lab11/PlugWatch/powerwatch/hardware/plugwatch_D/board/README.md

# Electron Sensor Board Rev 4
This sensor board is part of the [GridWatch](http://grid.watch) project.

The goal of this board is to test data collection in Accra. It is an updated
version of revision 3 with a focus on reliable operation even with a lack
of power and cloud connectivity. Please reference revision three for more
information.
