lab11/PlugWatch/powerwatch/firmware/particle/plugwatch_F/README.md

Plugwatch F Firmware
====================

We are building and deploying 400 of Plugwatch F.

It is hardware revision 1 in the versioning system (i.e. firmwares starting at 000100).

With plugwatch F the data format changes to include voltage and test whether the device
is plugged in or not.
