lab11/PlugWatch/powerwatch/cloud/kubernetes/grafana/README.md

Timescale
=================================

To deploy the grafana instance follow these steps:

## Setup a configuration file

```
$ kubectl create configmap grafana-provisioning --from-file=datasource.yaml --from-file=dashboard.yaml
$ kubectl create configmap grafana-dashboards --from-file=Powerwatch_General.json
```

## Add secrets

Modify the secrets files to add the database usernames and passwords

```
$ kubectl create -f ./grafana-config.yaml
```

## Deploy the cluster
```
$ kubectl create -f ./grafana-deployment.yaml
```
