lab11/PlugWatch/app/src/main/ic_launcher-web.png

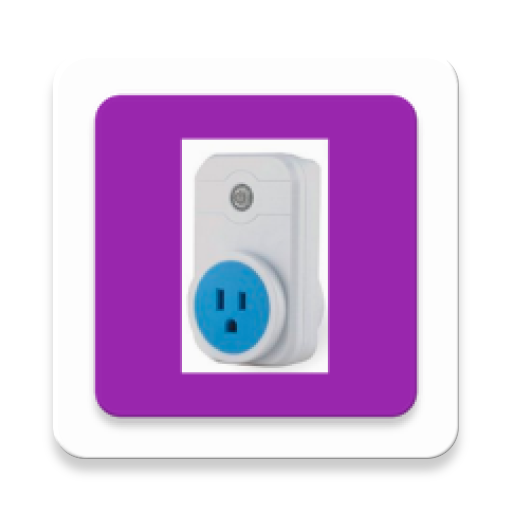
app/src/main/ic_launcher-web.png
