lab11/PlugWatch/powerwatch/deployment-tools/provision/base_tag.png

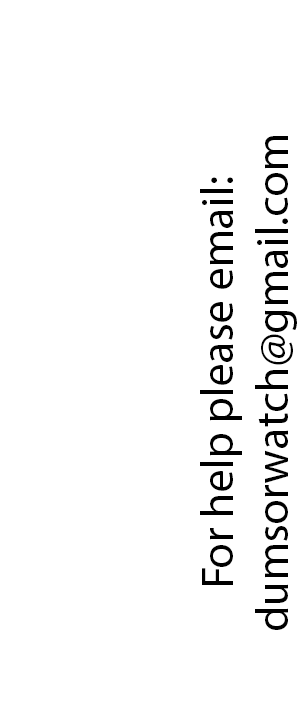
powerwatch/deployment-tools/provision/base_tag.png
