lab11/PlugWatch/powerwatch/deployment-tools/provision/wit/code.png

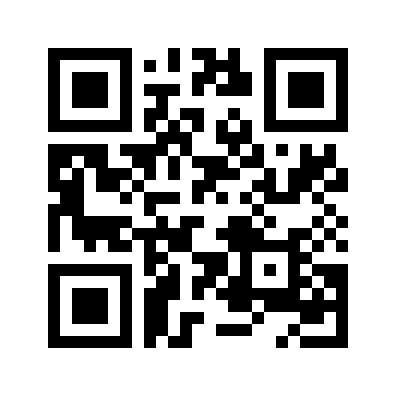
powerwatch/deployment-tools/provision/wit/code.png
