lab11/PlugWatch/powerwatch/hardware/electron_rev_1/board_image.png

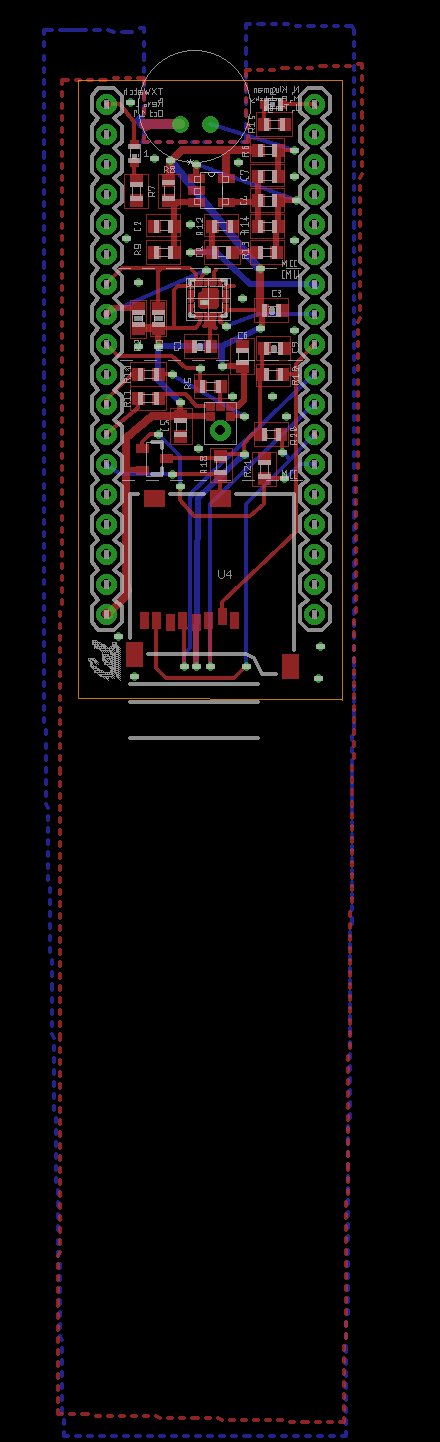
powerwatch/hardware/electron_rev_1/board_image.png
