lab11/PlugWatch/powerwatch/hardware/plugwatch_E/board/plugwatch_pcb.png

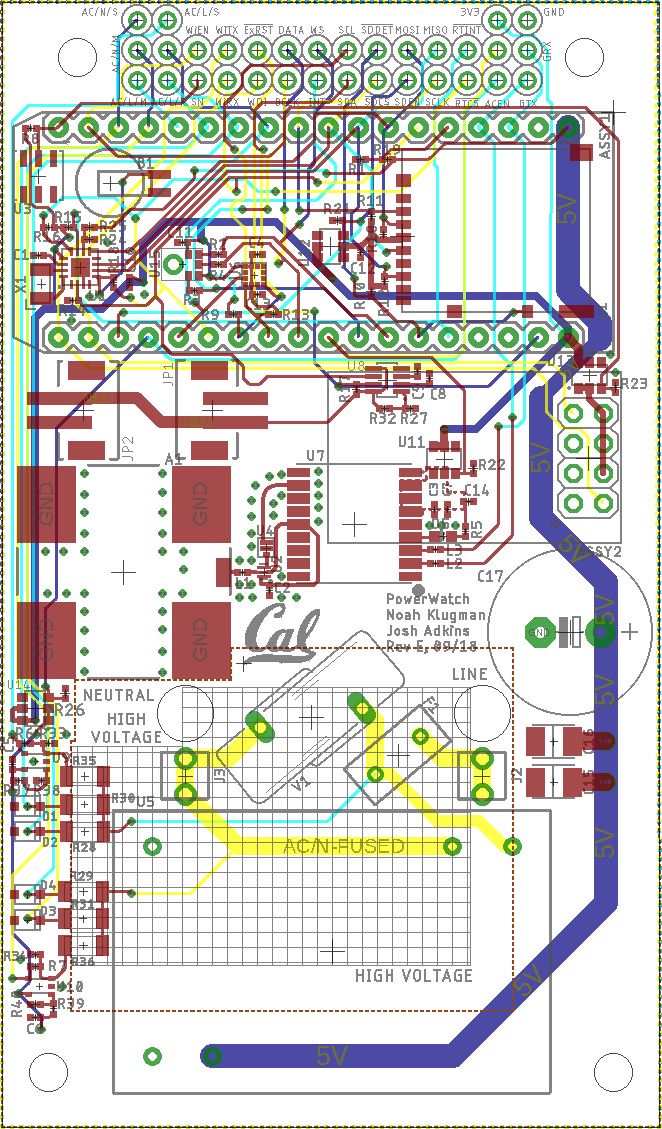
powerwatch/hardware/plugwatch_E/board/plugwatch_pcb.png
