lab11/PlugWatch/powerwatch/hardware/electron_rev_1/orders/costs.xlsx

Order | Cost | Submitted | Reimbursed | Shipment Expected | Received | Item | Num Units | Per Unit | Total
Particle | 1332.38 | No | No | unknown | No | particles | 15 | 170.8206667 | 2562.31
Sparkfun | 275.75 | No | No | 25th | No | sd sockets, test parts, gas sensors
Digikey | 349.75 | No | No |  | No | resistors, capacitors, imu, microphones, op-amps, mosfets
PCB | 237 | No | No |  | No | 15 circuit boards
Amazon | 237.44 | No | No | 22nd | 22nd | sd cards
Particle | 129.99 | No | No | Preorder | No | enterprise eval kit
