lab11/PlugWatch/powerwatch/hardware/electron_rev_1/orders/amazon_order.png

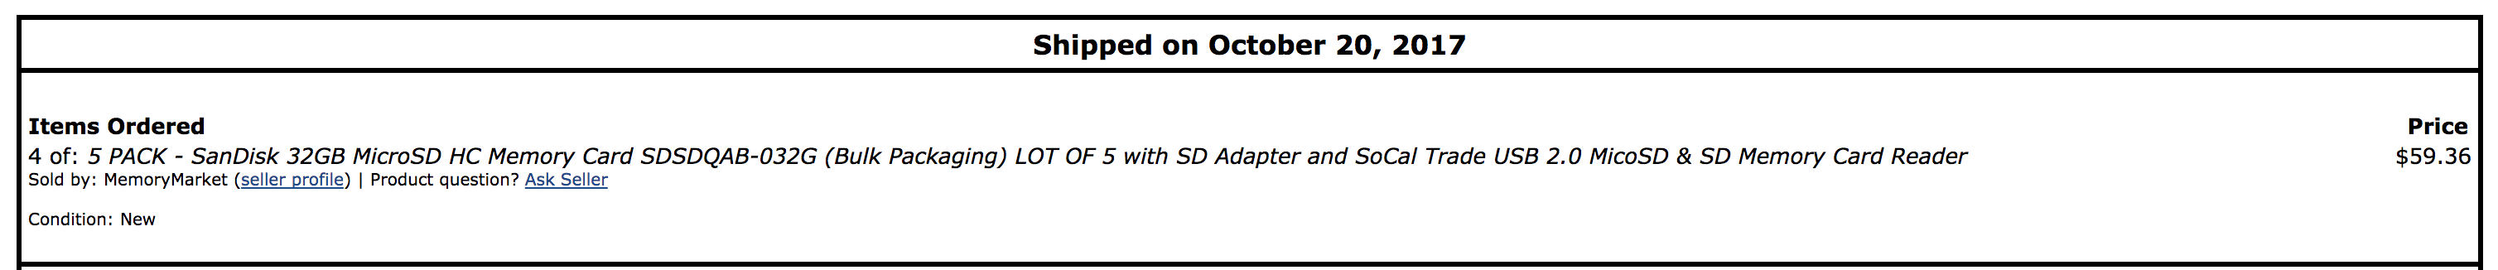
powerwatch/hardware/electron_rev_1/orders/amazon_order.png
