lab11/PlugWatch/powerwatch/hardware/plugwatch_B/case/particle_base.SLDPRT

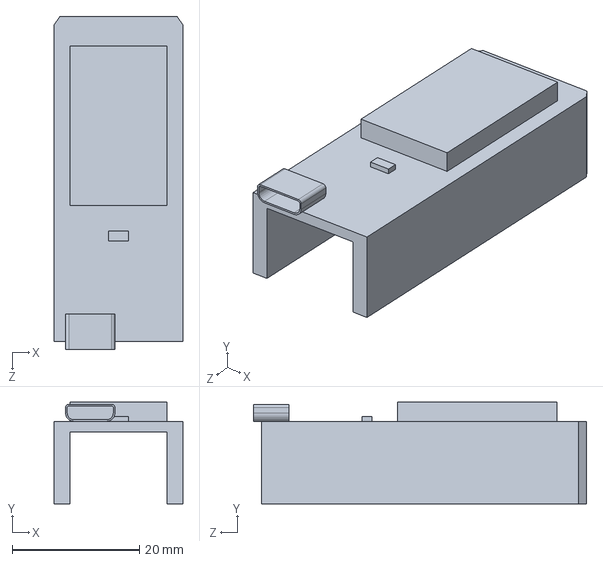
[picture p25: CAD file, 2018-01-17]
powerwatch/hardware/plugwatch_B/case/particle_base.SLDPRT
20.2 x 16.0 x 52.2 mm
