lab11/PlugWatch/powerwatch/hardware/plugwatch_B/case/battery.SLDPRT

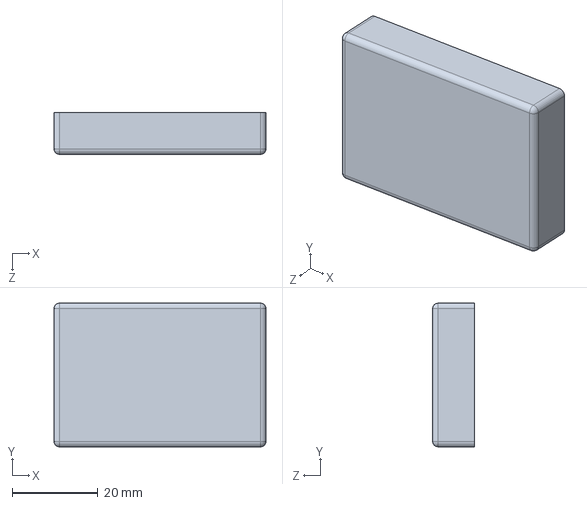
[picture p26: CAD file, 2018-01-17]
powerwatch/hardware/plugwatch_B/case/battery.SLDPRT
49.4 x 33.5 x 9.73 mm
