lab11/PlugWatch/powerwatch/hardware/plugwatch_D/board/plugwatch.pdf

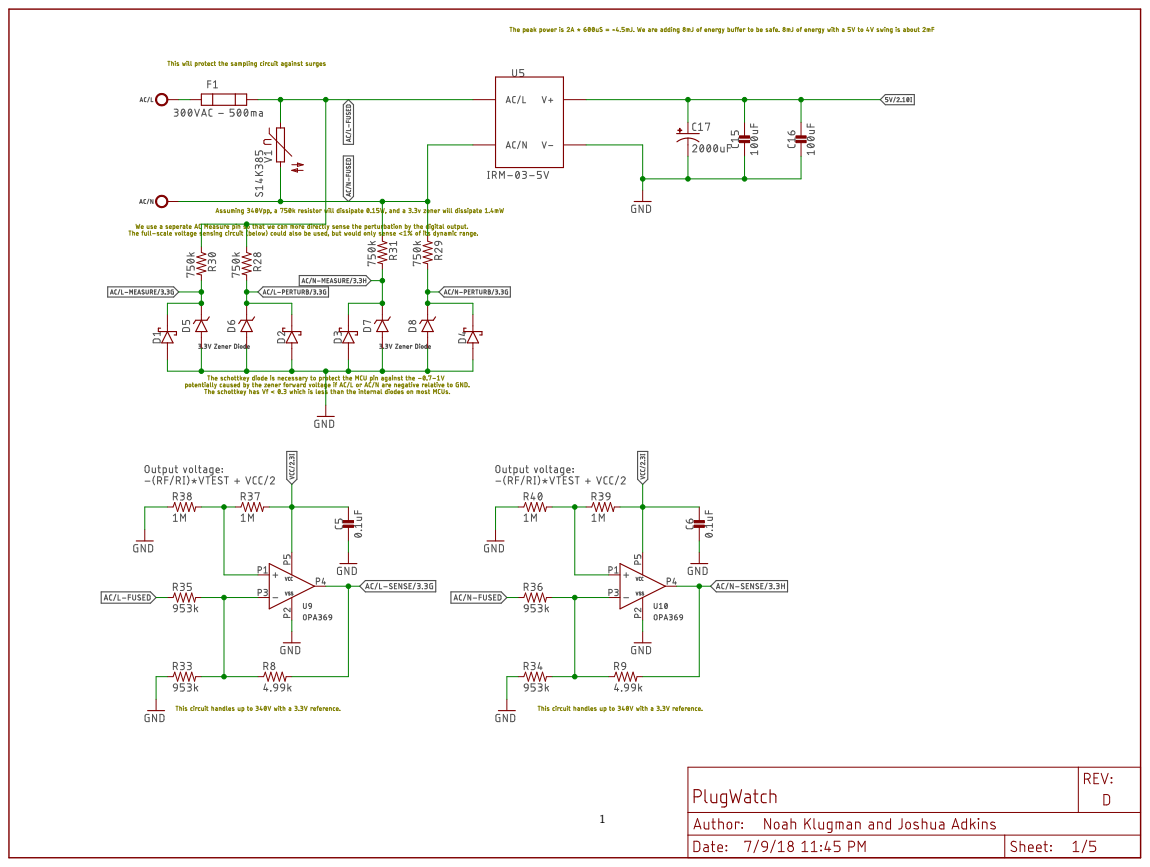
[picture p64: page 1]

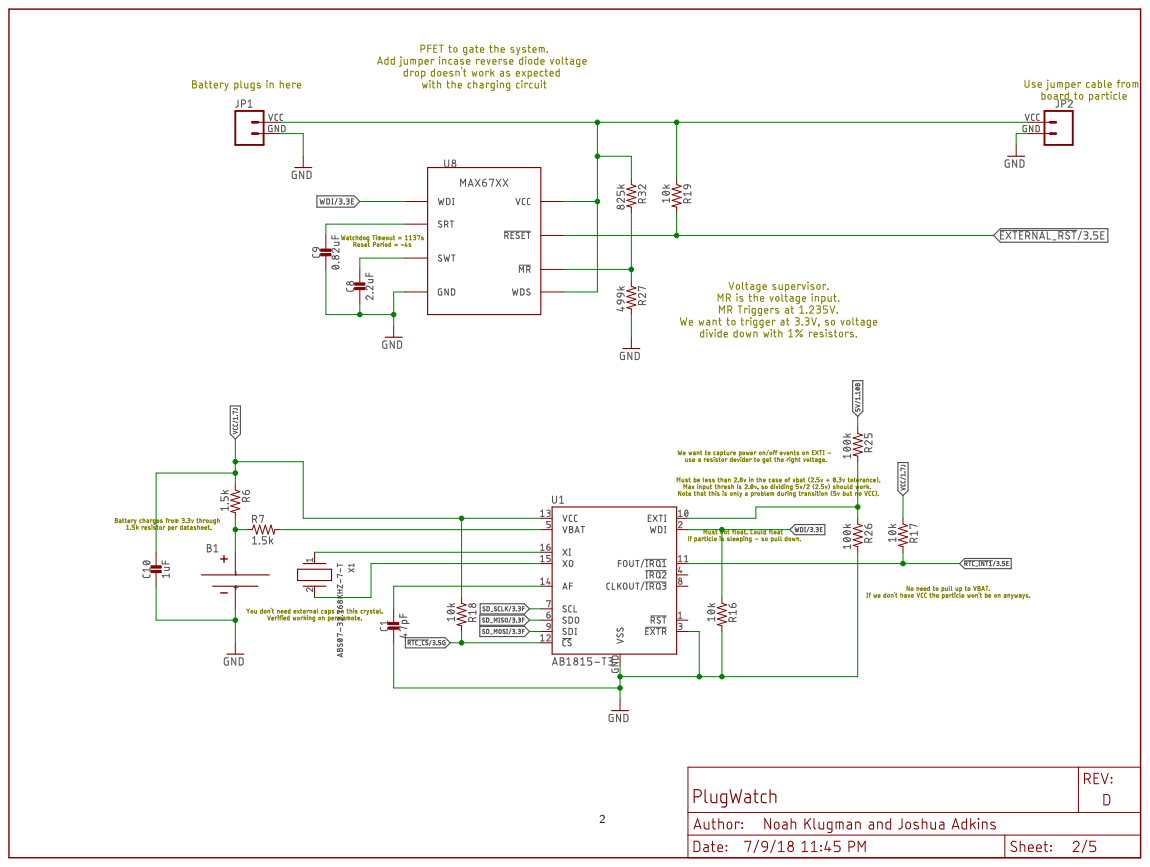
[picture p65: page 2]

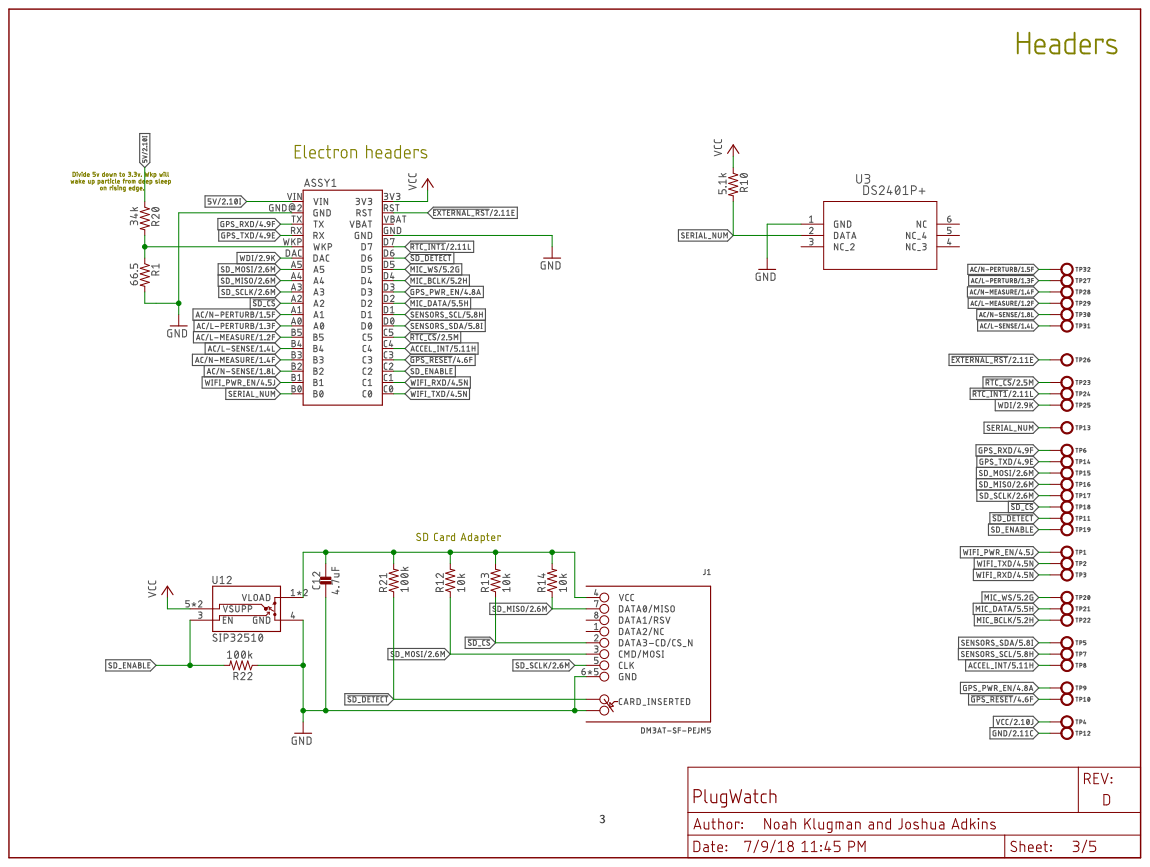
[picture p66: page 3]

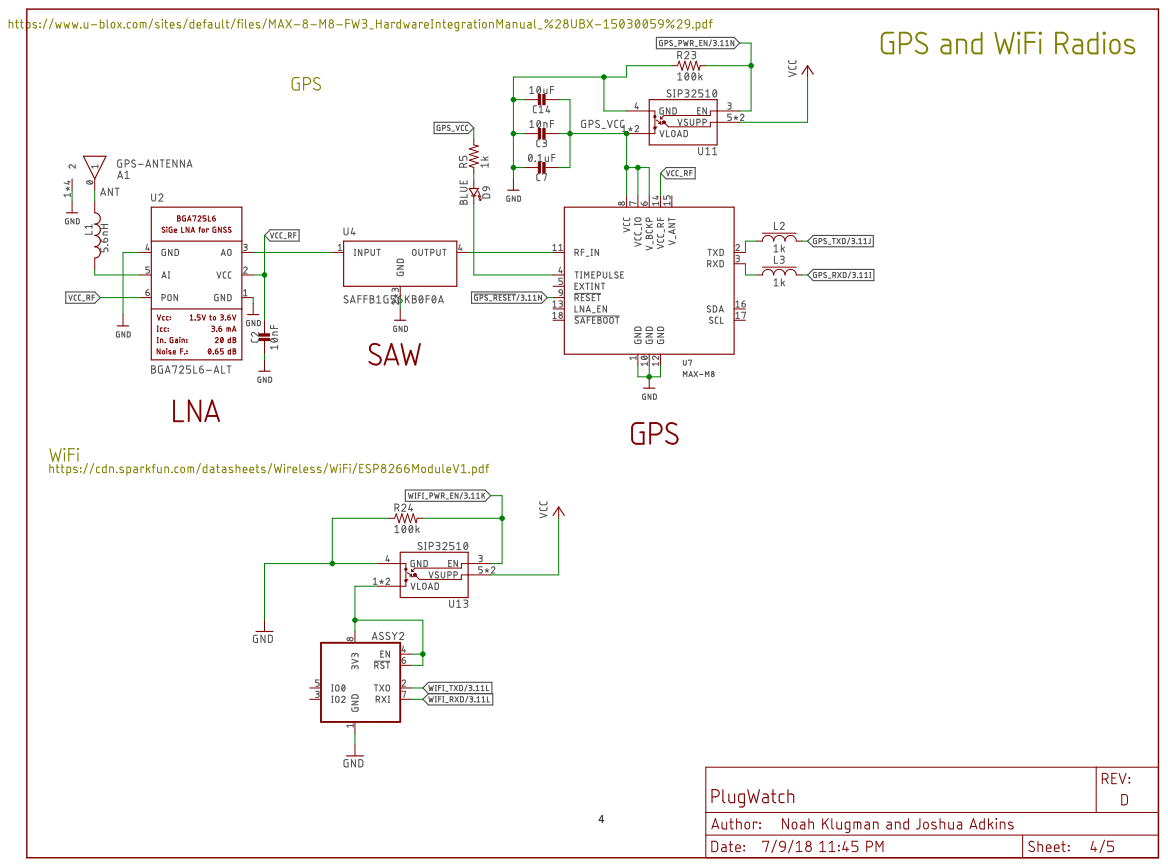
[picture p67: page 4]

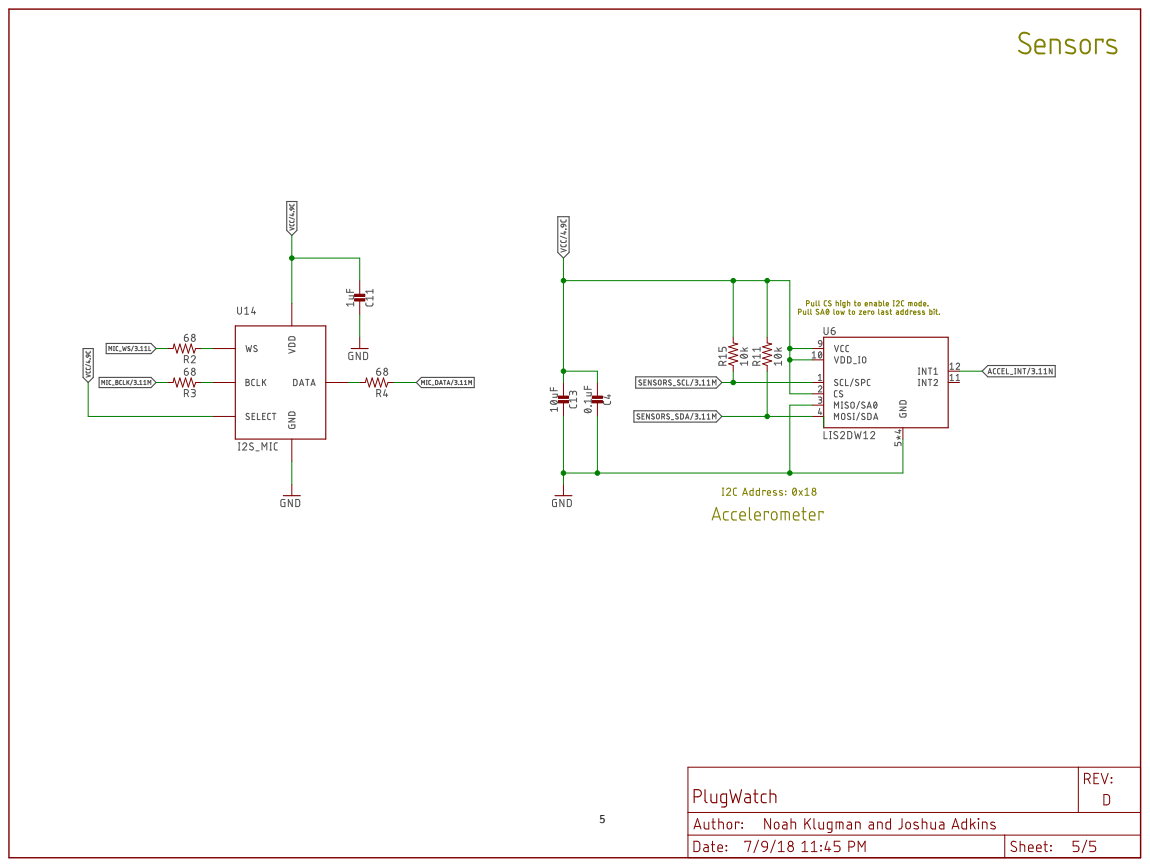
[picture p68: page 5]

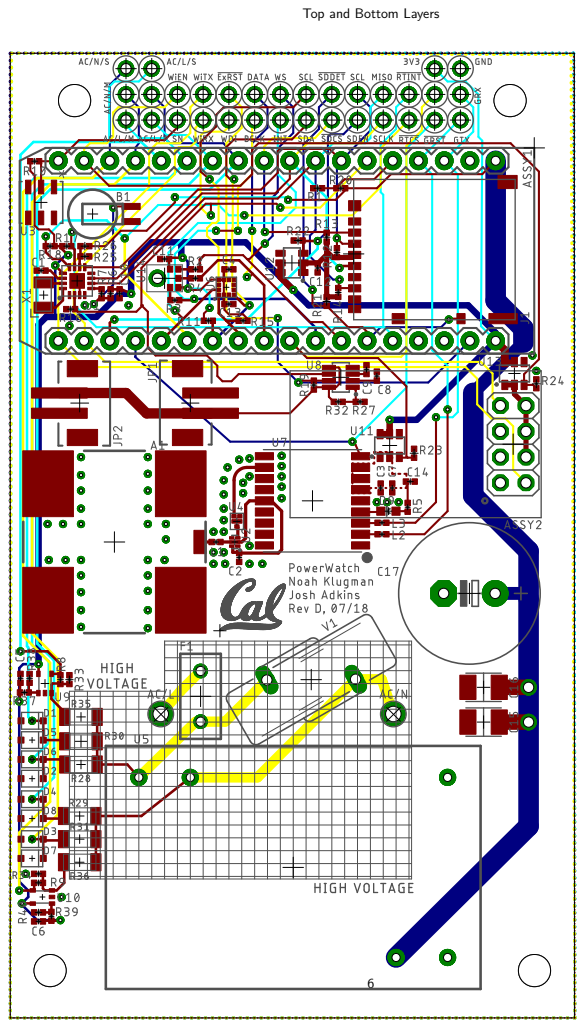
[picture p69: page 6]

Top and Bottom Layers

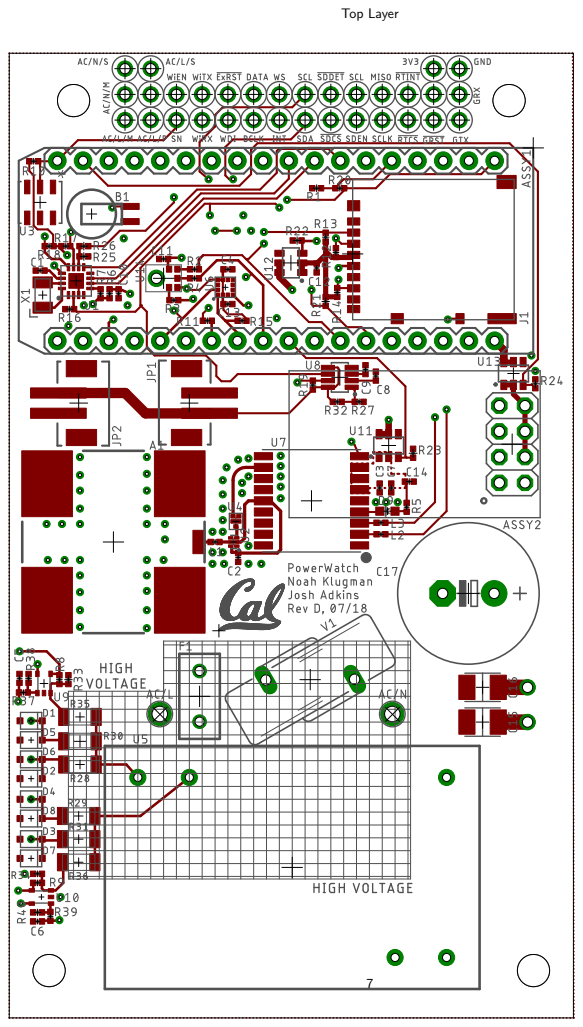
[picture p70: page 7]
Top Layer

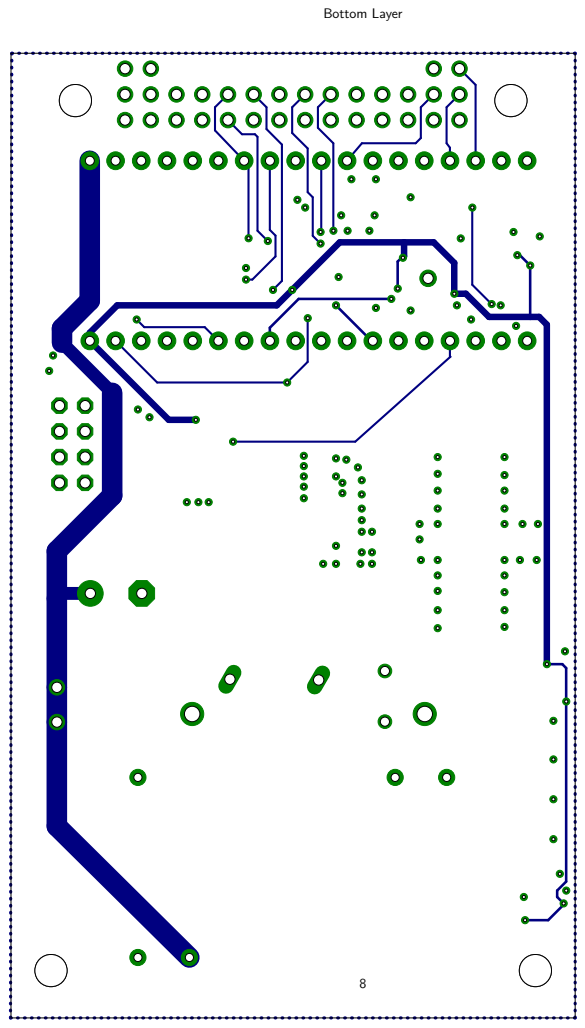
[picture p71: page 8]
Bottom Layer

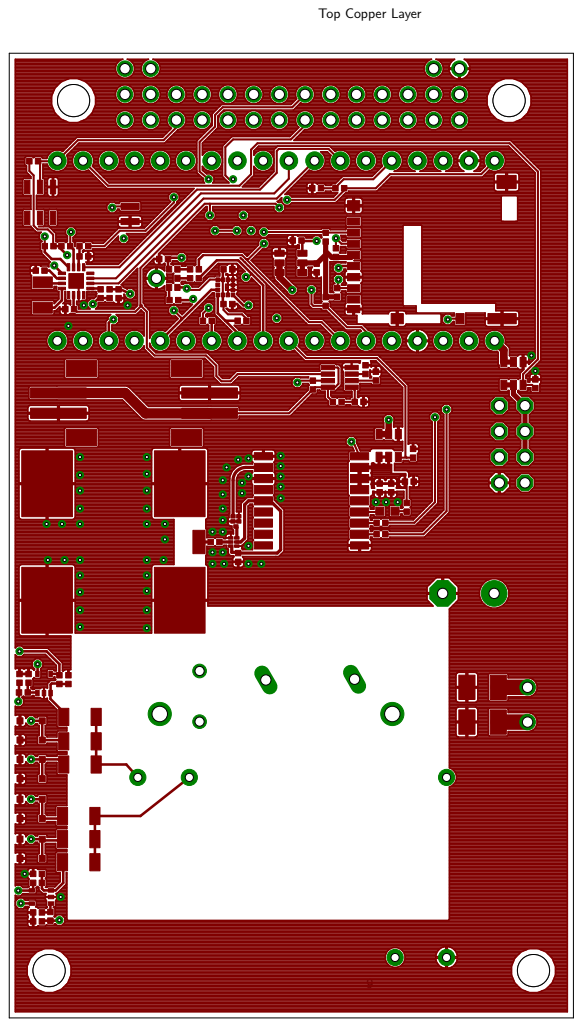
[picture p72: page 9]

Top Copper Layer

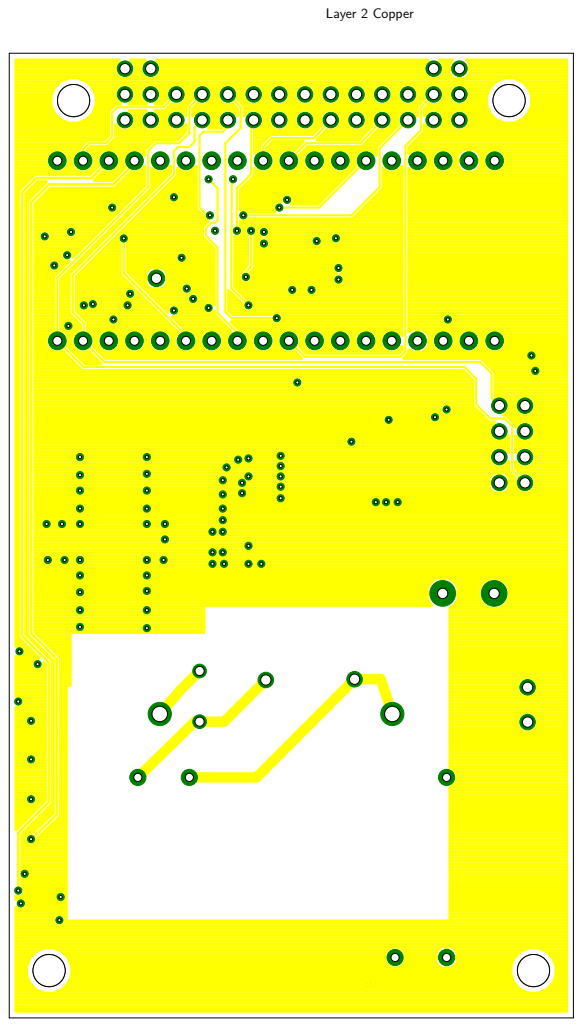
[picture p73: page 10]
Layer 2 Copper

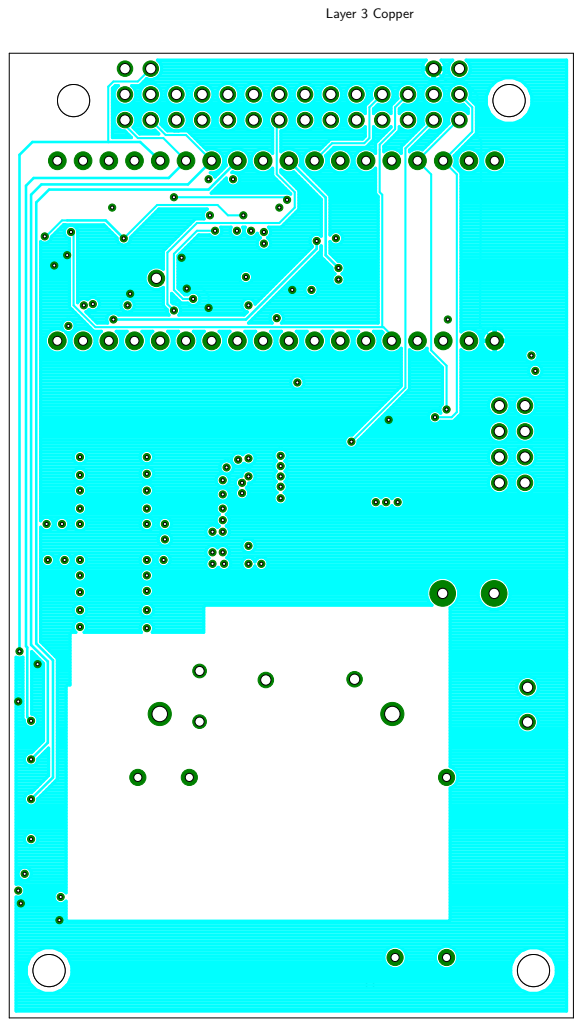
[picture p74: page 11]
Layer 3 Copper

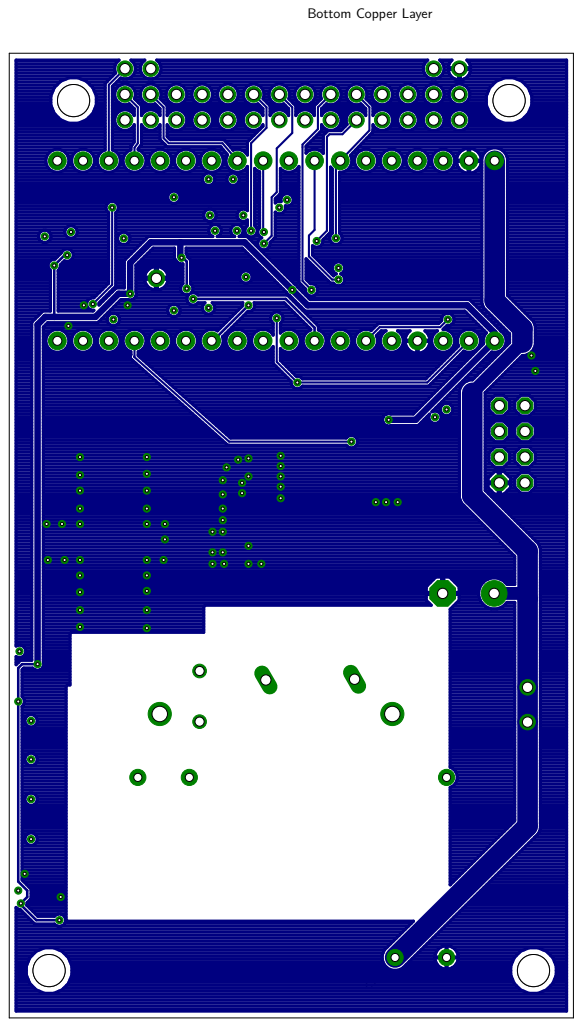
[picture p75: page 12]

Bottom Copper Layer

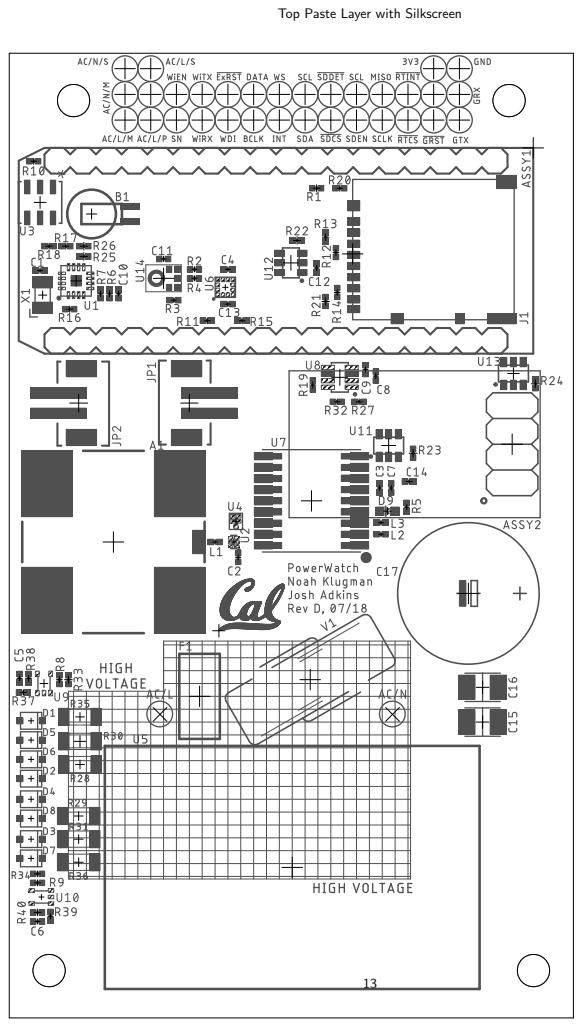
[picture p76: page 13]

Top Paste Layer with Silkscreen

Bottom Paste Layer with Silkscreen

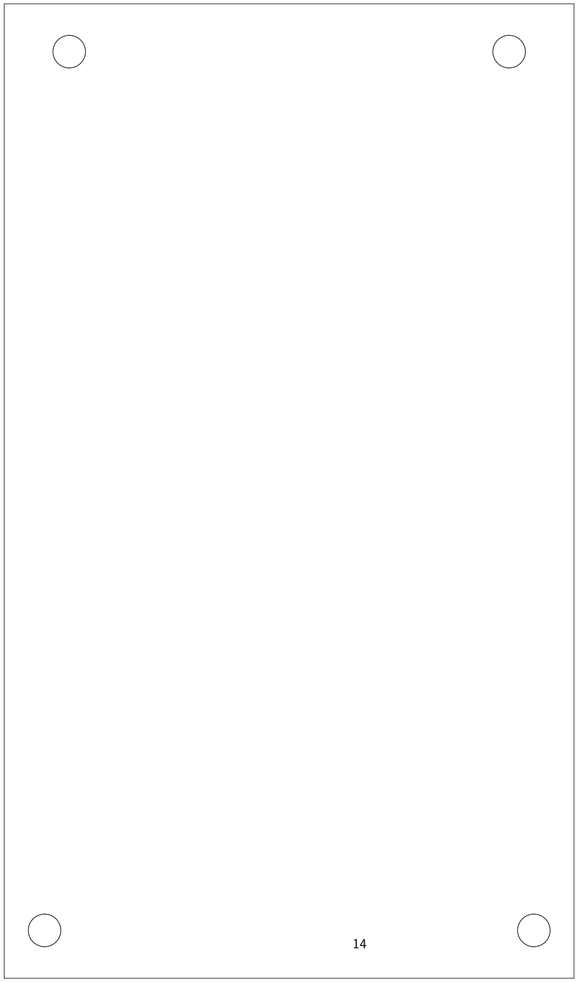
[picture p77: figure]
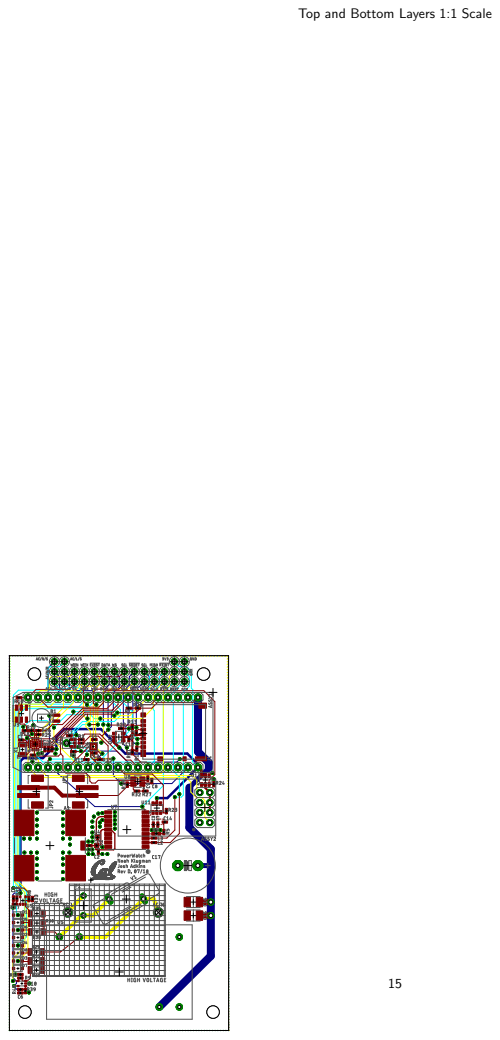
[picture p78: page 15]

Top and Bottom Layers 1:1 Scale

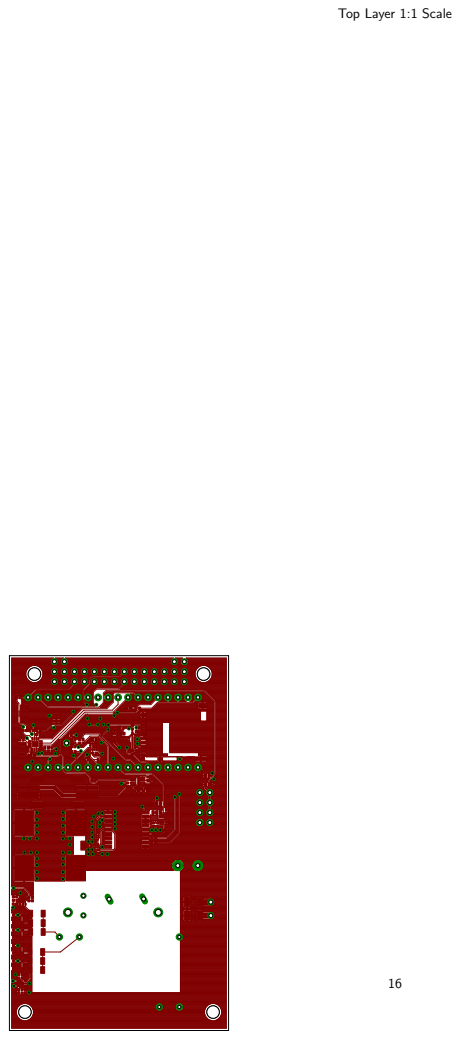
[picture p79: page 16]

Top Layer 1:1 Scale

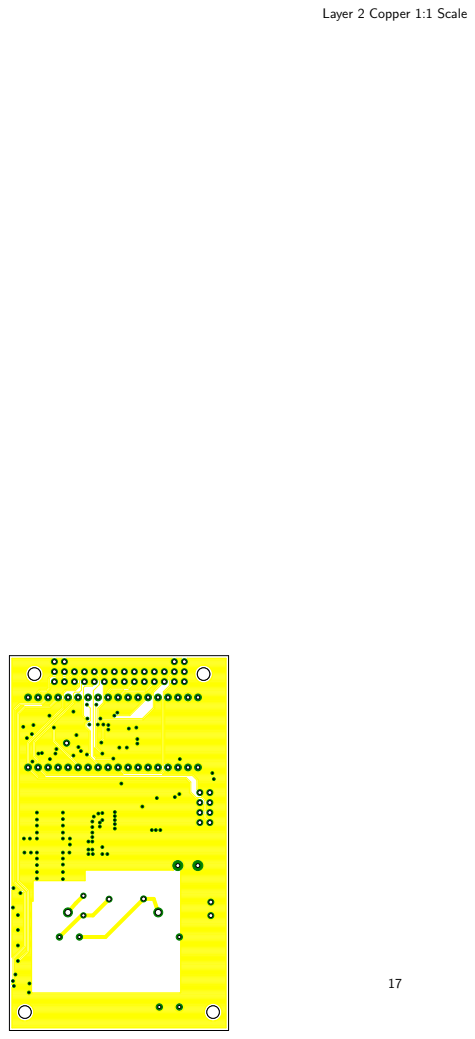
[picture p80: page 17]

Layer 2 Copper 1:1 Scale

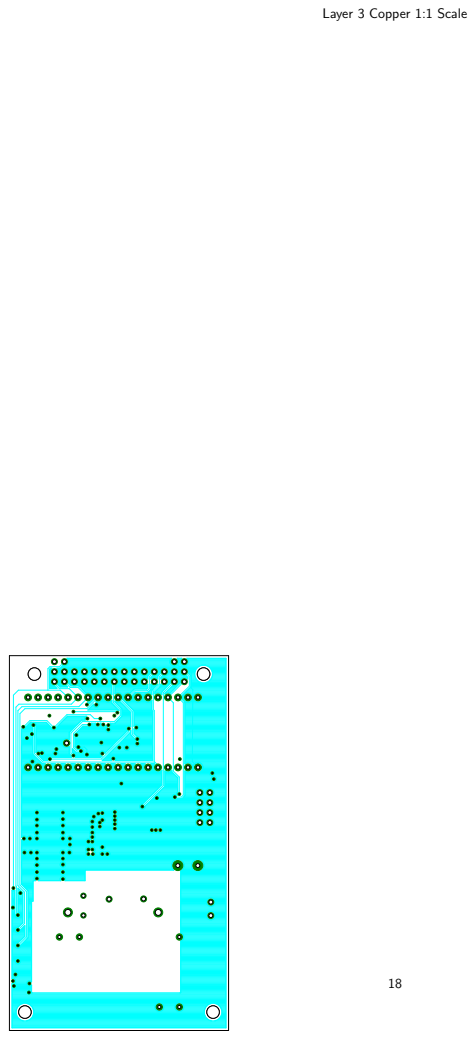
[picture p81: page 18]

Layer 3 Copper 1:1 Scale

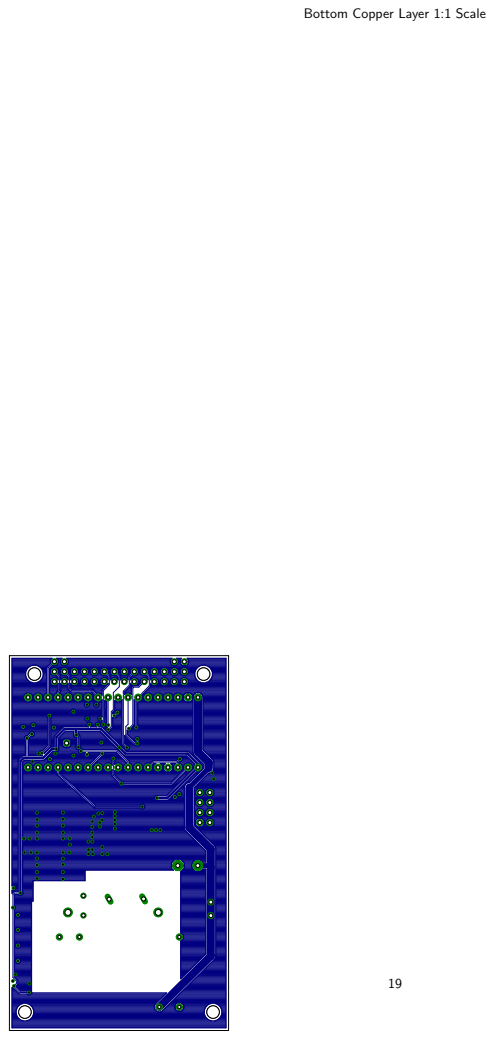
[picture p82: page 19]

Bottom Copper Layer 1:1 Scale
