lab11/PlugWatch/Data/kplc_interruption/Interruptions/Special_Interruption_in_Western_Kenya.pdf

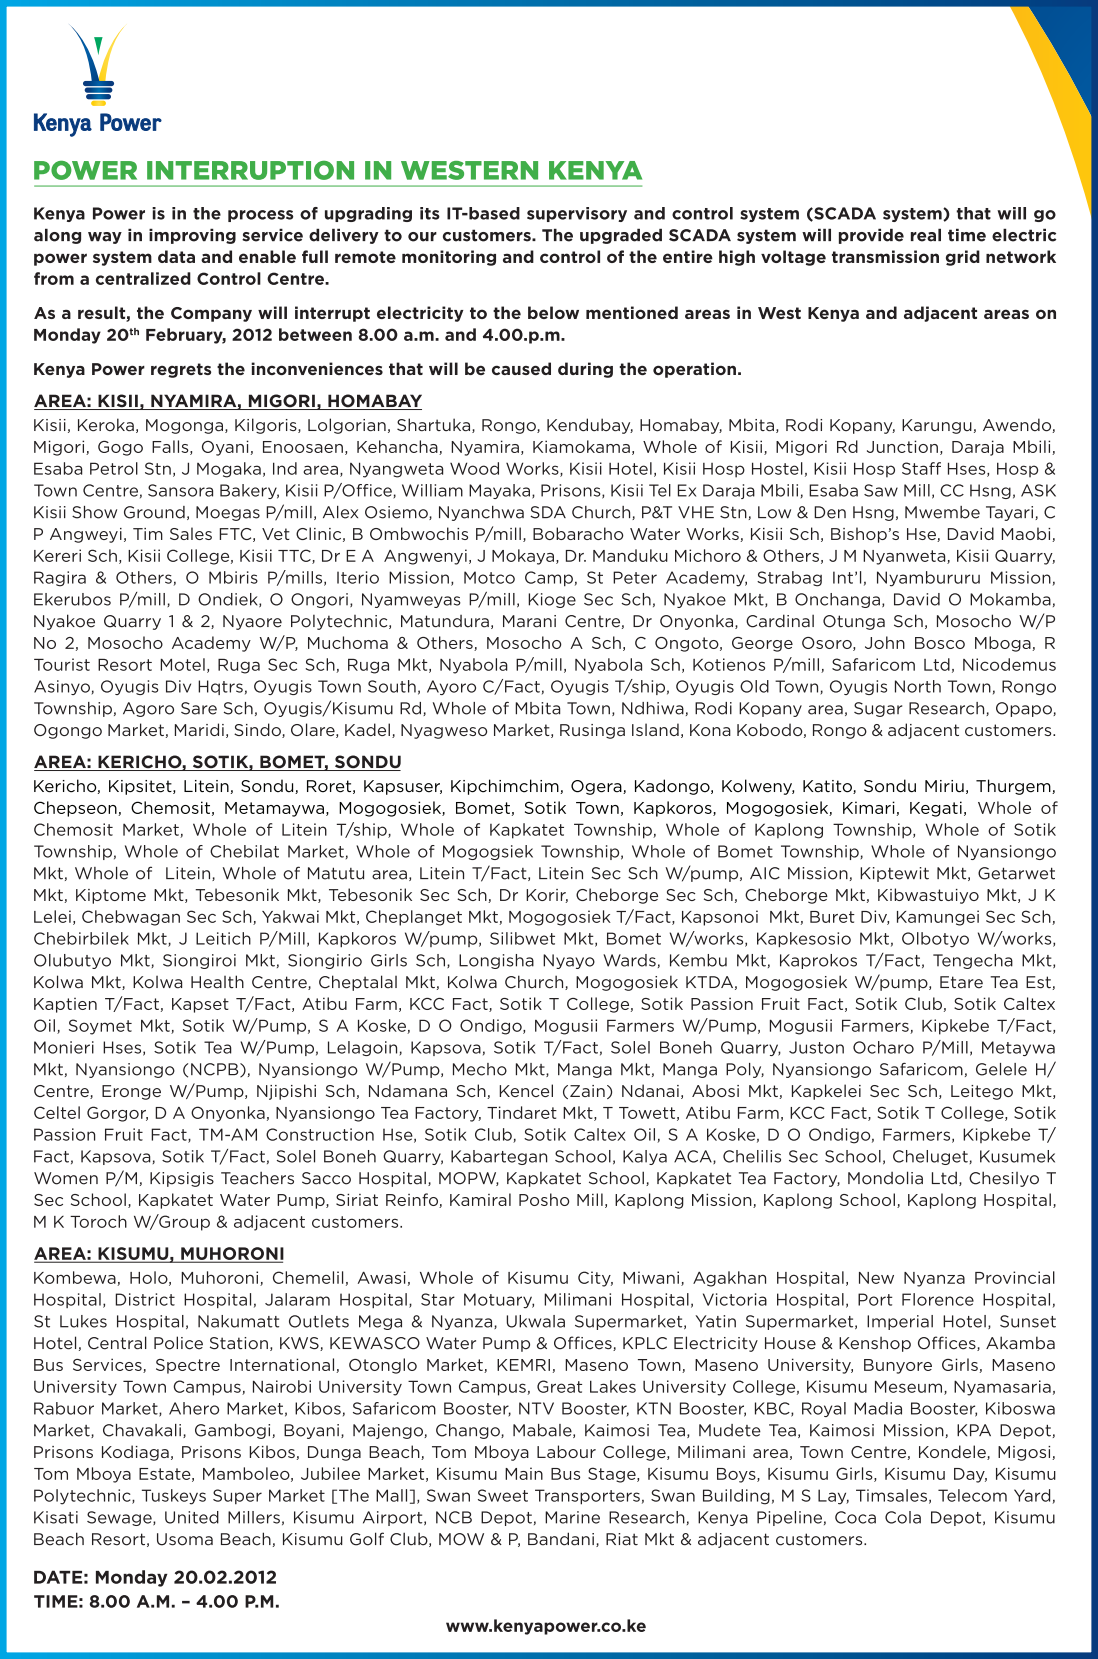
[picture p124: page 1]
