lab11/PlugWatch/Data/kplc_interruption/interruptions_from_website/Special Power Interruption Notice - Magadi & Industrial Area - 24.11.2016.pdf

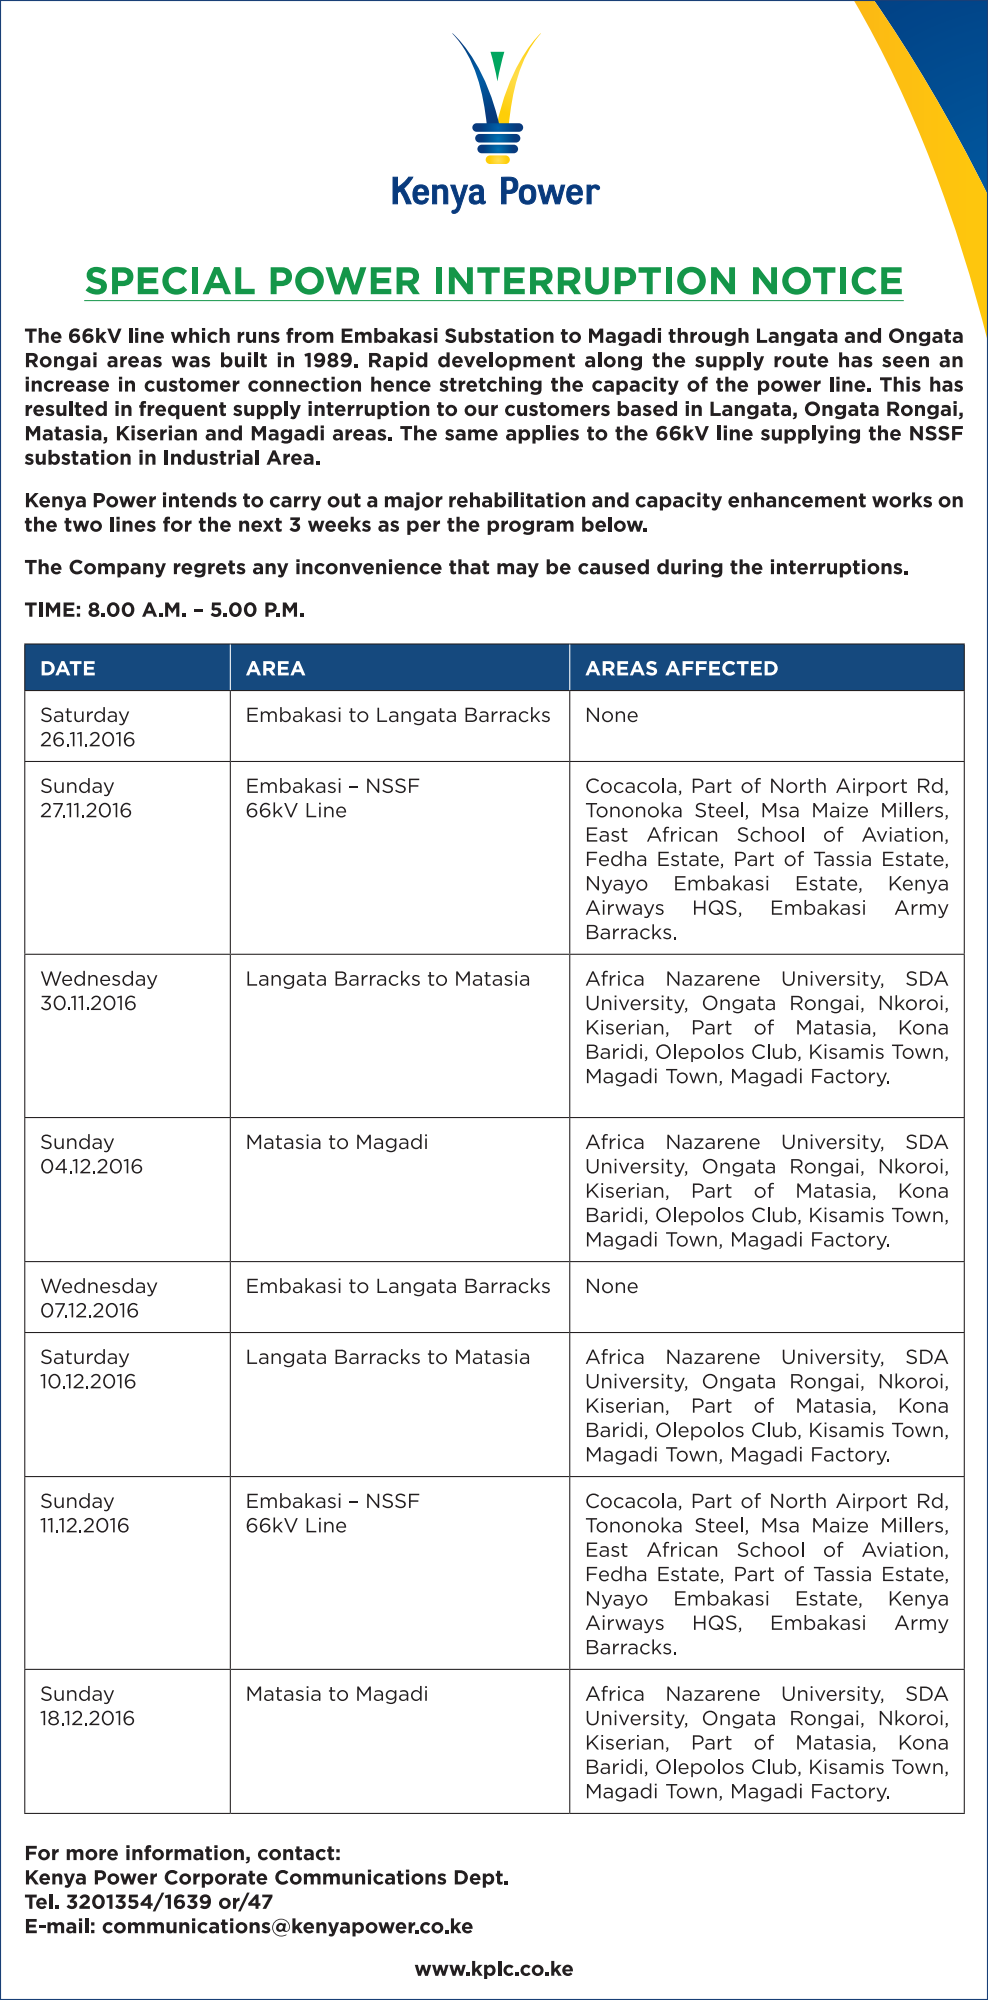
[picture p125: page 1]
