lab11/PlugWatch/powerwatch/hardware/plugwatch_B/case/s-series-02-12(12).PDF

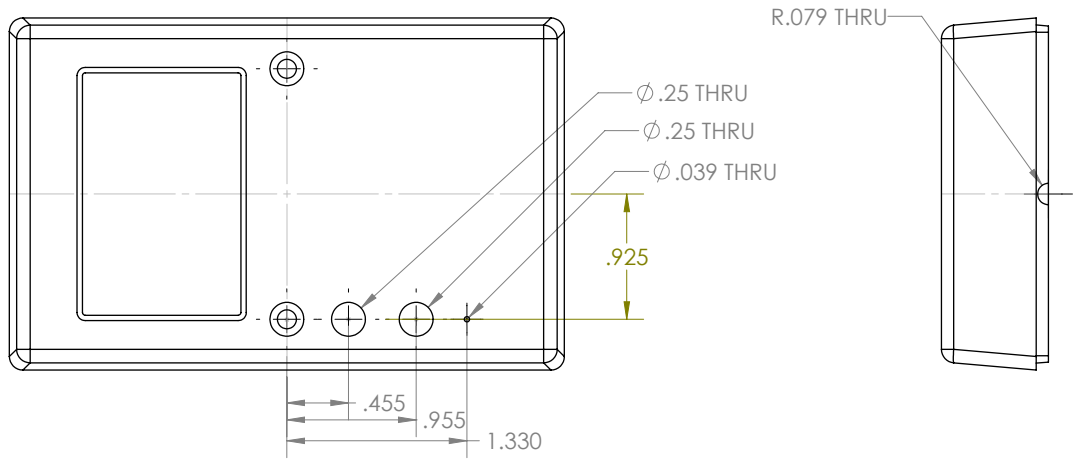
[picture p126: page 1]
.25 THRU .25 THRU .039 THRU; R.079 THRU

SOLIDWORKS Educational Product. For Instructional Use Only.
