lab11/PlugWatch/powerwatch/hardware/plugwatch_B/case/S-series-2X-Top(2-2)-1.PDF

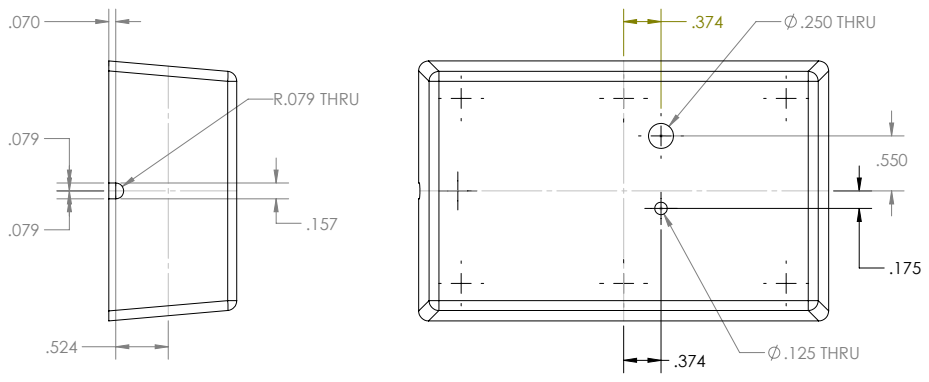
[picture p127: page 1]
.250 THRU; .125 THRU; R.079 THRU

SOLIDWORKS Educational Product. For Instructional Use Only.
