lab11/PlugWatch/Data/kplc_interruption/interruptions_from_website/to_strip/5HljXmKmGIQW_Special Interruption - Outering Road.pdf

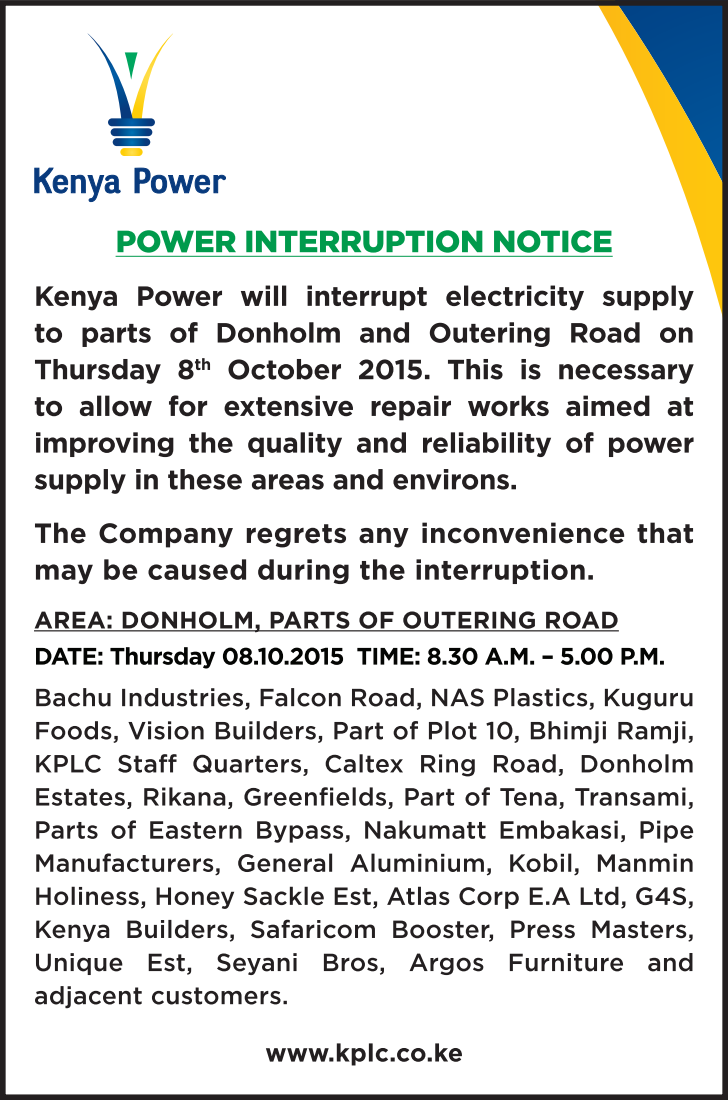
[picture p128: page 1]
