lab11/PlugWatch/Data/kplc_interruption/Interruptions/02.01.2012.PDF

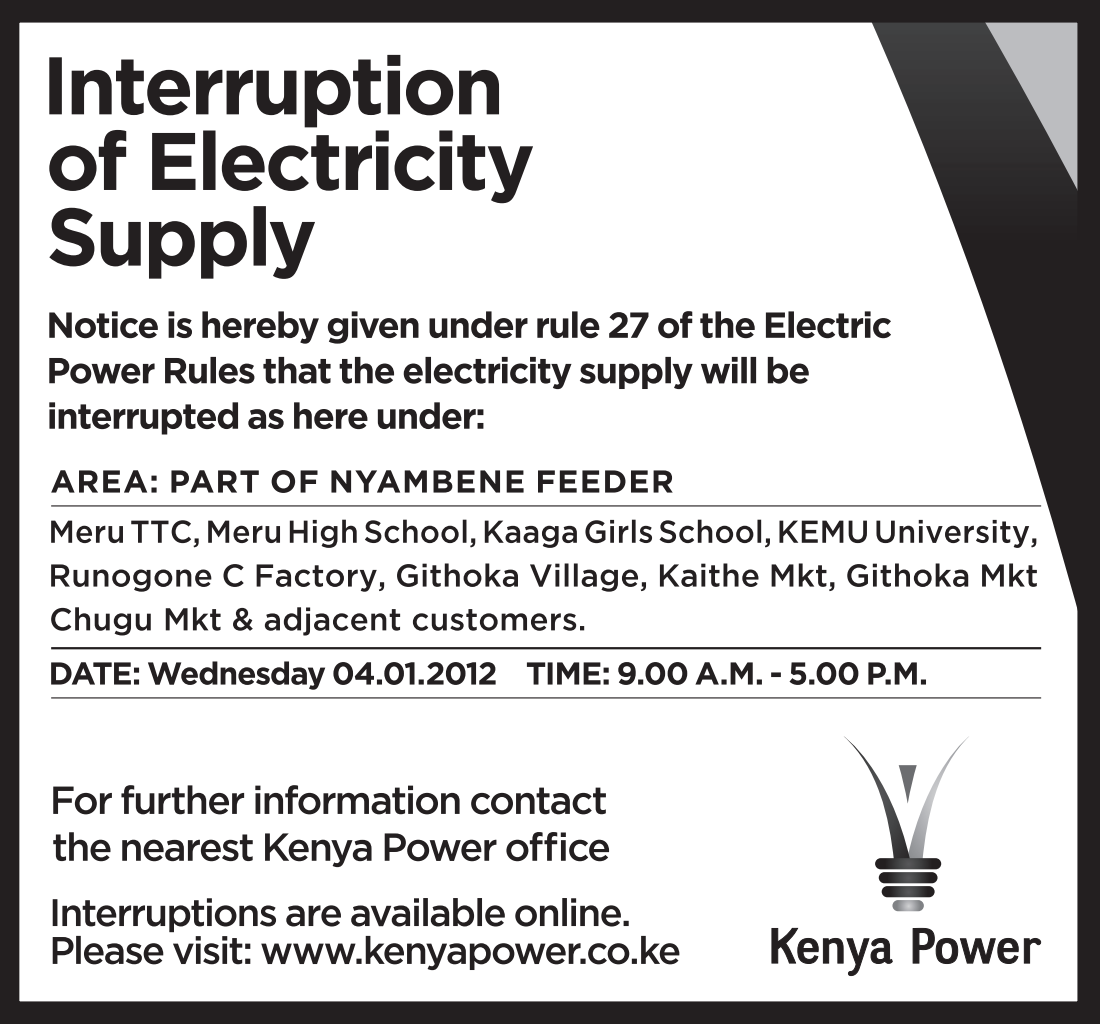
[picture p129: page 1]
