lab11/PlugWatch/Data/kplc_interruption/Interruptions/02.02.2012.PDF

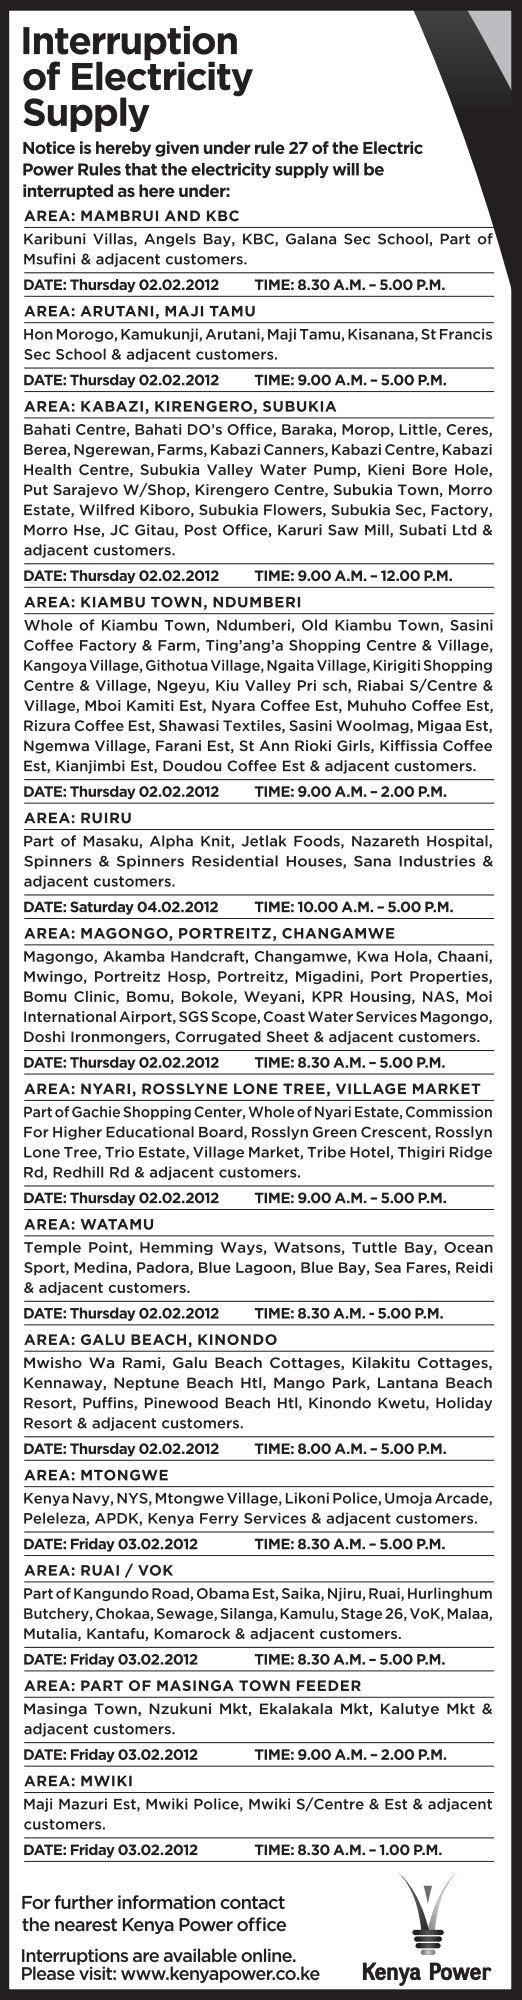
[picture p130: page 1]

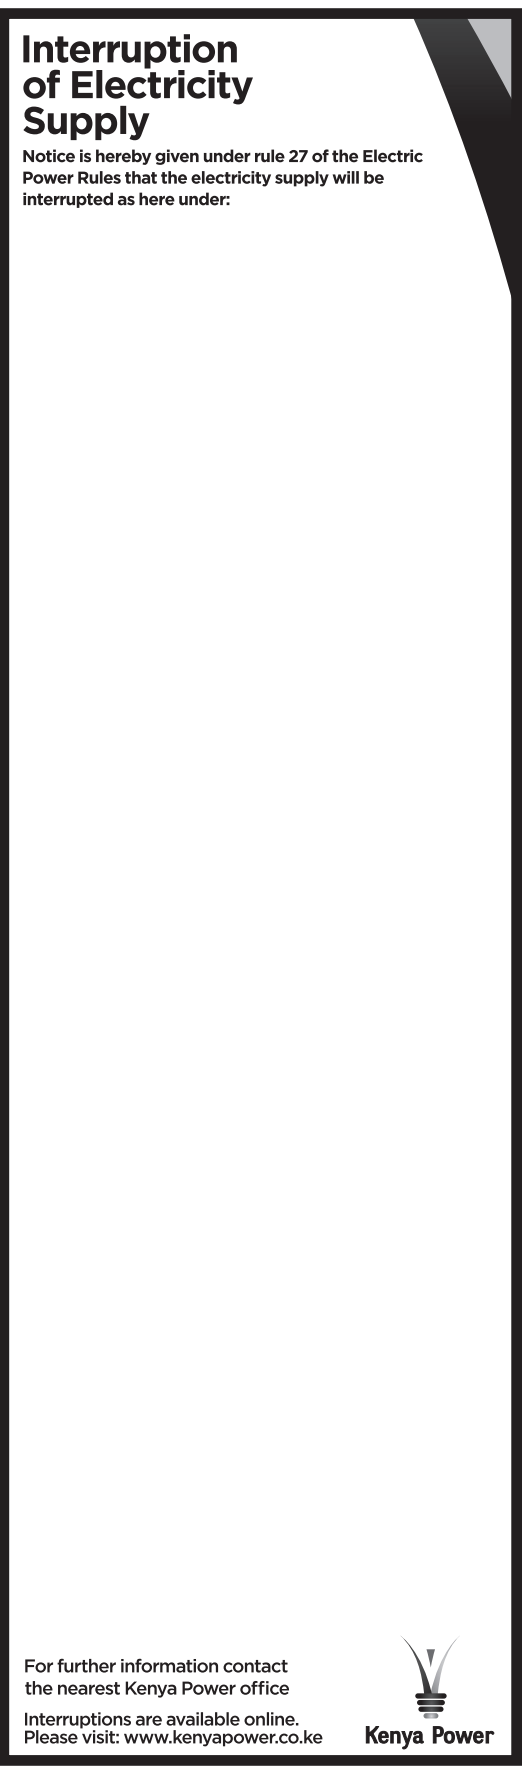
[picture p131: page 2]
