lab11/PlugWatch/Data/kplc_interruption/Interruptions/02.12.2011.pdf

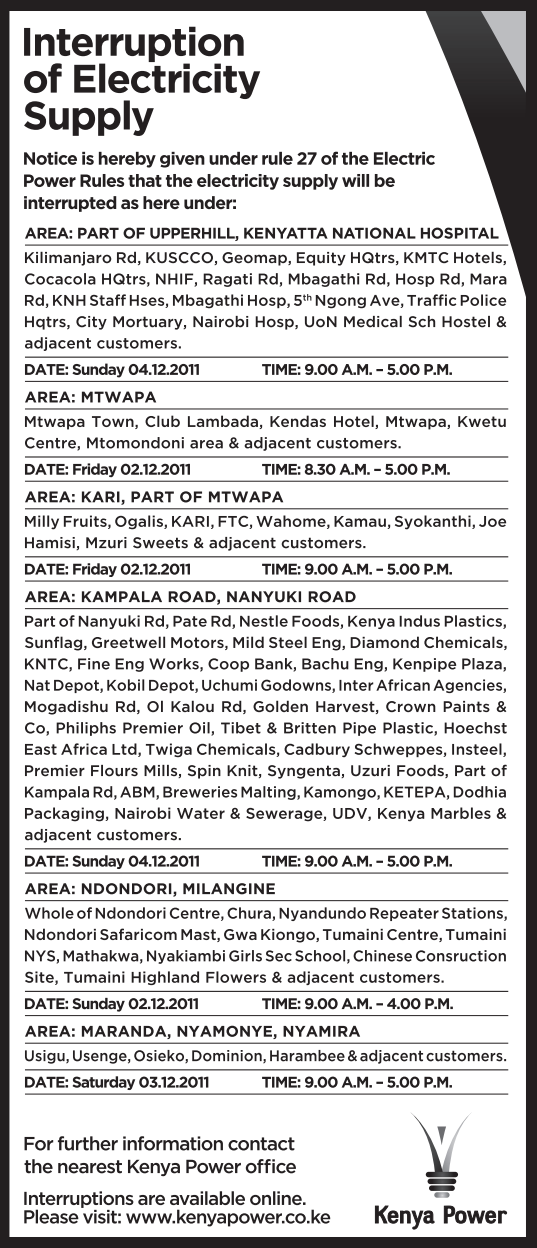
[picture p132: page 1]
