lab11/PlugWatch/Data/kplc_interruption/Interruptions/03.01.2012.PDF

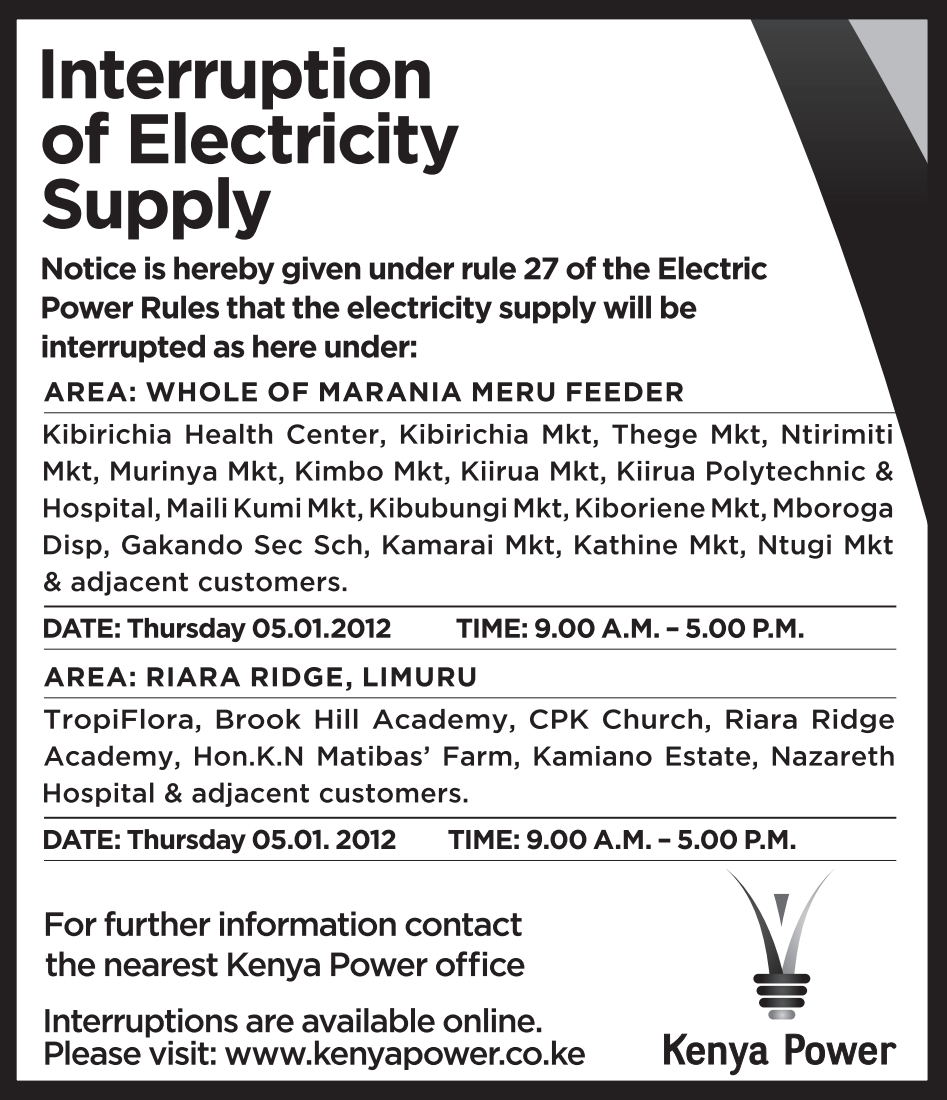
[picture p133: page 1]
