lab11/PlugWatch/powerwatch/firmware/particle/plugwatch_F/firmware/src/ChargeState.h

#pragma once

#include <Particle.h>

#include "FileLog.h"
#include "Subsystem.h"

/* Checks charging state at `frequency`. Publishes every change. */
class ChargeState: public Subsystem {
  typedef Subsystem super;

  String result;

public:
  const String CHARGE_STATE_BATTERY = "b";
  const String CHARGE_STATE_WALL = "w";

  void setup();
  LoopStatus loop();
  String getResult();
};
