lab11/PlugWatch/powerwatch/firmware/particle/plugwatch_F/firmware/src/Subsystem.h

#pragma once

#include <Particle.h>

enum LoopStatus {
  FinishedSuccess,
  FinishedError,
  NotFinished,
};

class Subsystem {
public:
  virtual void setup();

  virtual LoopStatus loop();

  virtual String getResult();
};
