lab11/PlugWatch/powerwatch/firmware/particle/plugwatch_F/firmware/src/AB1815.h

#pragma once

#include <Particle.h>

#define AB1815_CS C5
#define AB1815_TIME_DATE_REG 0x00
#define AB1815_CFG_KEY_REG 0x1F
#define AB1815_TRICKLE_REG 0x20

#define AB1815_SECOND_TENS_MASK     0x70
#define AB1815_SECOND_TENS_OFFSET   4
#define AB1815_SECOND_ONES_MASK     0x0F
#define AB1815_SECOND_ONES_OFFSET   0

#define AB1815_MINUTE_TENS_MASK     0x70
#define AB1815_MINUTE_TENS_OFFSET   4
#define AB1815_MINUTE_ONES_MASK     0x0F
#define AB1815_MINUTE_ONES_OFFSET   0

#define AB1815_HOUR_TENS_MASK     0x30
#define AB1815_HOUR_TENS_OFFSET   4
#define AB1815_HOUR_ONES_MASK     0x0F
#define AB1815_HOUR_ONES_OFFSET   0

#define AB1815_DAY_TENS_MASK     0x30
#define AB1815_DAY_TENS_OFFSET   4
#define AB1815_DAY_ONES_MASK     0x0F
#define AB1815_DAY_ONES_OFFSET   0

#define AB1815_MON_TENS_MASK     0x10
#define AB1815_MON_TENS_OFFSET   4
#define AB1815_MON_ONES_MASK     0x0F
#define AB1815_MON_ONES_OFFSET   0

#define AB1815_YEAR_TENS_MASK     0xF0
#define AB1815_YEAR_TENS_OFFSET   4
#define AB1815_YEAR_ONES_MASK     0x0F
#define AB1815_YEAR_ONES_OFFSET   0

class AB1815 {
public:
   void     init();
   void     setTime(uint32_t unixTime);
   uint32_t getTime(void);
};
