lab11/PlugWatch/powerwatch/firmware/particle/plugwatch_F/firmware/src/Imu.h

#pragma once

#include <Particle.h>

#include "lis2dh12.h"
#include "Subsystem.h"

#define IMU_INT C4

class Imu: public Subsystem {
  typedef Subsystem super;

  String self_test_str;

  String result;

public:
  lis2dh12 accel;
  void setup();
  LoopStatus loop();
  String getResult();
};
