lab11/PlugWatch/powerwatch/firmware/particle/plugwatch_F/firmware/src/FileLog.h

//***********************************
//* SD Log Instance Variables / Functions
//***********************************

#pragma once

#include <queue>

#define MINOR_DLIM "|"
#define MAJOR_DLIM ";"

class SDCard;
//retained char current_name[50];

class FileLog {
  SDCard &sd;
  String filename;

  std::queue<String> isr_queue;

public:
	FileLog(SDCard &sd, String filename, char* current_name) : sd{sd}, filename{filename}, current_name{current_name} {}

  // Only print to Serial
  void debugFromISR(String str);
  void debug(String str);

  // Print to serial and log to SD
  void appendFromISR(String str);
  bool append(String str);

  // Print to serial, log to SD, publish to cloud
  void errorFromISR(String str);
  bool error(String str);

  // Get size
  int getFileSize();

  String getCurrentName();

private:
  void processIsrQueue();
  char* current_name;
};
