lab11/PlugWatch/powerwatch/firmware/particle/plugwatch_B/validation/mpu/src/mpu-test.ino

#include "quaternionFilters.h"
#include "MPU9250.h"
#include "Particle.h"

#define AHRS false         // Set to false for basic data read
#define SerialDebug true  // Set to true to get Serial output for debugging

// Pin definitions
int intPin = A1;  // These can be changed, 2 and 3 are the Arduinos ext int pins
int myLed  = B0;  // Set up pin 13 led for toggling

SYSTEM_MODE(MANUAL);


MPU9250 myIMU;

void setup()
{
  Wire.begin();
  Serial.begin(38400);

  // Set up the  pin, its set as active high, push-pull
  pinMode(intPin, OUTPUT);
  pinMode(myLed, OUTPUT);

  // Read the WHO_AM_I register, this is a good test of communication
  byte c = myIMU.readByte(MPU9250_ADDRESS, WHO_AM_I_MPU9250);
  Serial.print("MPU9250 "); Serial.print("I AM "); Serial.print(c, HEX);
  Serial.print(" I should be "); Serial.println(0x71, HEX);

  if (c == 0x71) // WHO_AM_I should always be 0x68
  {
    Serial.println("MPU9250 is online...");

    // Start by performing self test and reporting values
    myIMU.MPU9250SelfTest(myIMU.SelfTest);
    Serial.print("x-axis self test: acceleration trim within : ");
    Serial.print(myIMU.SelfTest[0],1); Serial.println("% of factory value");
    Serial.print("y-axis self test: acceleration trim within : ");
    Serial.print(myIMU.SelfTest[1],1); Serial.println("% of factory value");
    Serial.print("z-axis self test: acceleration trim within : ");
    Serial.print(myIMU.SelfTest[2],1); Serial.println("% of factory value");
    Serial.print("x-axis self test: gyration trim within : ");
    Serial.print(myIMU.SelfTest[3],1); Serial.println("% of factory value");
    Serial.print("y-axis self test: gyration trim within : ");
    Serial.print(myIMU.SelfTest[4],1); Serial.println("% of factory value");
    Serial.print("z-axis self test: gyration trim within : ");
    Serial.print(myIMU.SelfTest[5],1); Serial.println("% of factory value");

    // Calibrate gyro and accelerometers, load biases in bias registers
    myIMU.calibrateMPU9250(myIMU.gyroBias, myIMU.accelBias);

    myIMU.initMPU9250();
    // Initialize device for active mode read of acclerometer, gyroscope, and
    // temperature
    Serial.println("MPU9250 initialized for active data mode....");

    // Read the WHO_AM_I register of the magnetometer, this is a good test of
    // communication
    byte d = myIMU.readByte(AK8963_ADDRESS, WHO_AM_I_AK8963);
    Serial.print("AK8963 "); Serial.print("I AM "); Serial.print(d, HEX);
    Serial.print(" I should be "); Serial.println(0x48, HEX);

    // Get magnetometer calibration from AK8963 ROM
    myIMU.initAK8963(myIMU.magCalibration);
    // Initialize device for active mode read of magnetometer
    Serial.println("AK8963 initialized for active data mode....");
    if (SerialDebug)
    {
      //  Serial.println("Calibration values: ");
      Serial.print("X-Axis sensitivity adjustment value ");
      Serial.println(myIMU.magCalibration[0], 2);
      Serial.print("Y-Axis sensitivity adjustment value ");
      Serial.println(myIMU.magCalibration[1], 2);
      Serial.print("Z-Axis sensitivity adjustment value ");
      Serial.println(myIMU.magCalibration[2], 2);
    }
  } // if (c == 0x71)
  else
  {
    Serial.print("Could not connect to MPU9250: 0x");
    Serial.println(c, HEX);
    while(1) ; // Loop forever if communication doesn't happen
  }
}

void loop()
{
  // If intPin goes high, all data registers have new data
  // On interrupt, check if data ready interrupt
  if (myIMU.readByte(MPU9250_ADDRESS, INT_STATUS) & 0x01)
  {
    myIMU.readAccelData(myIMU.accelCount);  // Read the x/y/z adc values
    myIMU.getAres();

    // Now we'll calculate the accleration value into actual g's
    // This depends on scale being set
    myIMU.ax = (float)myIMU.accelCount[0]*myIMU.aRes; // - accelBias[0];
    myIMU.ay = (float)myIMU.accelCount[1]*myIMU.aRes; // - accelBias[1];
    myIMU.az = (float)myIMU.accelCount[2]*myIMU.aRes; // - accelBias[2];

    myIMU.readGyroData(myIMU.gyroCount);  // Read the x/y/z adc values
    myIMU.getGres();

    // Calculate the gyro value into actual degrees per second
    // This depends on scale being set
    myIMU.gx = (float)myIMU.gyroCount[0]*myIMU.gRes;
    myIMU.gy = (float)myIMU.gyroCount[1]*myIMU.gRes;
    myIMU.gz = (float)myIMU.gyroCount[2]*myIMU.gRes;

    myIMU.readMagData(myIMU.magCount);  // Read the x/y/z adc values
    myIMU.getMres();
    // User environmental x-axis correction in milliGauss, should be
    // automatically calculated
    myIMU.magbias[0] = +470.;
    // User environmental x-axis correction in milliGauss TODO axis??
    myIMU.magbias[1] = +120.;
    // User environmental x-axis correction in milliGauss
    myIMU.magbias[2] = +125.;

    // Calculate the magnetometer values in milliGauss
    // Include factory calibration per data sheet and user environmental
    // corrections
    // Get actual magnetometer value, this depends on scale being set
    myIMU.mx = (float)myIMU.magCount[0]*myIMU.mRes*myIMU.magCalibration[0] -
               myIMU.magbias[0];
    myIMU.my = (float)myIMU.magCount[1]*myIMU.mRes*myIMU.magCalibration[1] -
               myIMU.magbias[1];
    myIMU.mz = (float)myIMU.magCount[2]*myIMU.mRes*myIMU.magCalibration[2] -
               myIMU.magbias[2];
  } // if (readByte(MPU9250_ADDRESS, INT_STATUS) & 0x01)

  // Must be called before updating quaternions!
  myIMU.updateTime();

  // Sensors x (y)-axis of the accelerometer is aligned with the y (x)-axis of
  // the magnetometer; the magnetometer z-axis (+ down) is opposite to z-axis
  // (+ up) of accelerometer and gyro! We have to make some allowance for this
  // orientationmismatch in feeding the output to the quaternion filter. For the
  // MPU-9250, we have chosen a magnetic rotation that keeps the sensor forward
  // along the x-axis just like in the LSM9DS0 sensor. This rotation can be
  // modified to allow any convenient orientation convention. This is ok by
  // aircraft orientation standards! Pass gyro rate as rad/s
  //  MadgwickQuaternionUpdate(ax, ay, az, gx*PI/180.0f, gy*PI/180.0f, gz*PI/180.0f,  my,  mx, mz);
  MahonyQuaternionUpdate(myIMU.ax, myIMU.ay, myIMU.az, myIMU.gx*DEG_TO_RAD,
                         myIMU.gy*DEG_TO_RAD, myIMU.gz*DEG_TO_RAD, myIMU.my,
                         myIMU.mx, myIMU.mz, myIMU.deltat);


    myIMU.delt_t = millis() - myIMU.count;
    if (myIMU.delt_t > 0)
    {

      String imu = "";
      String x_accel_mg = String(1000*myIMU.ax);
      imu += ",";
      imu += x_accel_mg;
      String y_accel_mg = String(1000*myIMU.ay);
      imu += ",";
      imu += y_accel_mg;
      String z_accel_mg = String(1000*myIMU.az);
      imu += ",";
      imu += z_accel_mg;
      String x_gyro_ds = String(myIMU.gx);
      String y_gyro_ds = String(myIMU.gy);
      String z_gyro_ds = String(myIMU.gz);
      String x_mag_mg = String(myIMU.mx);
      String y_mag_mg = String(myIMU.my);
      String z_mag_mg = String(myIMU.mz);
      myIMU.tempCount = myIMU.readTempData();  // Read the adc values
      myIMU.temperature = ((float) myIMU.tempCount) / 333.87 + 21.0; // Temperature in degrees Centigrade
      String tmp_c = String(myIMU.temperature);

      myIMU.count = millis();
      //digitalWrite(myLed, !digitalRead(myLed));  // toggle led
    } // if (myIMU.delt_t > 0)
}
