lab11/PlugWatch/powerwatch/firmware/particle/plugwatch_C/sd_examples/src/sd_examples.ino

/*
 * Project sd_examples
 * Description:
 * Author:
 * Date:
 */

// setup() runs once, when the device is first turned on.
void setup() {
  // Put initialization like pinMode and begin functions here.

}

// loop() runs over and over again, as quickly as it can execute.
void loop() {
  // The core of your code will likely live here.

}
