lab11/PlugWatch/powerwatch/firmware/particle/plugwatch_B/validation/btn/src/btn-test.ino

#include "Particle.h"

SYSTEM_MODE(MANUAL);

const int buttonPin = A0;     // the number of the pushbutton pin
const int ledPin =  D7;      // the number of the LED pin
int buttonState = 0;         // variable for reading the pushbutton status

void setup() {
  pinMode(ledPin, OUTPUT);
  pinMode(buttonPin, INPUT);
}

void loop() {
  buttonState = digitalRead(buttonPin);
  if (buttonState == HIGH) {
    digitalWrite(ledPin, HIGH);
  } else {
    digitalWrite(ledPin, LOW);
  }
}
